gearfinity/gearfinity/planetary_gear_stage/planet_gear_sleeve_bearing-1.step

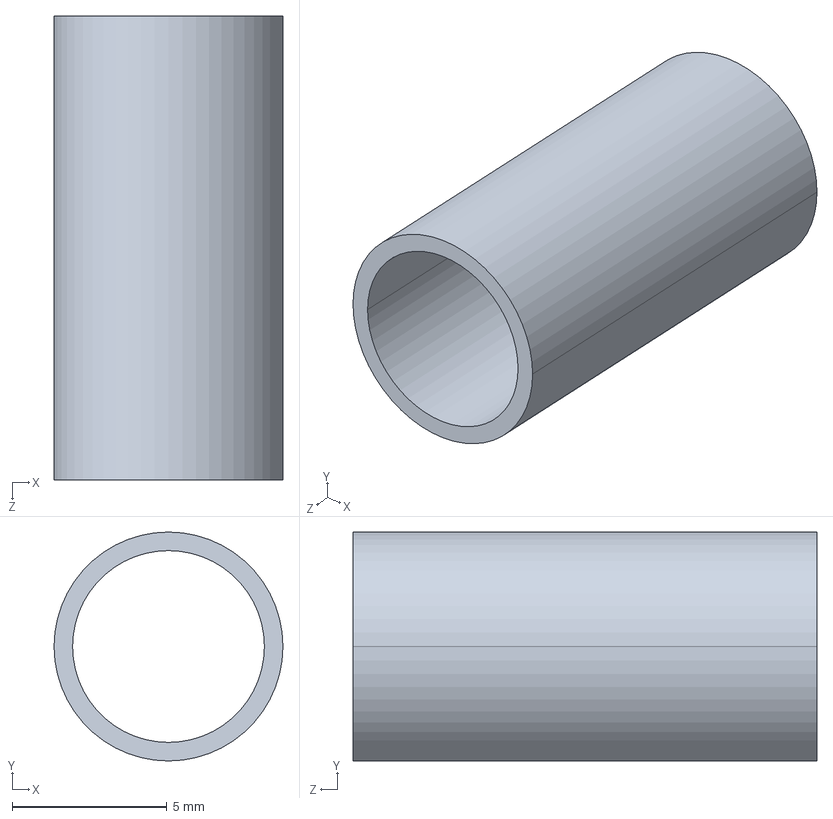
[picture p14: CAD file, 2023-09-10]
planetary_gear_stage/planet_gear_sleeve_bearing-1.step
7.40 x 7.40 x 15.0 mm
