gearfinity/gearfinity/fan_module/fan_cage-1.STL

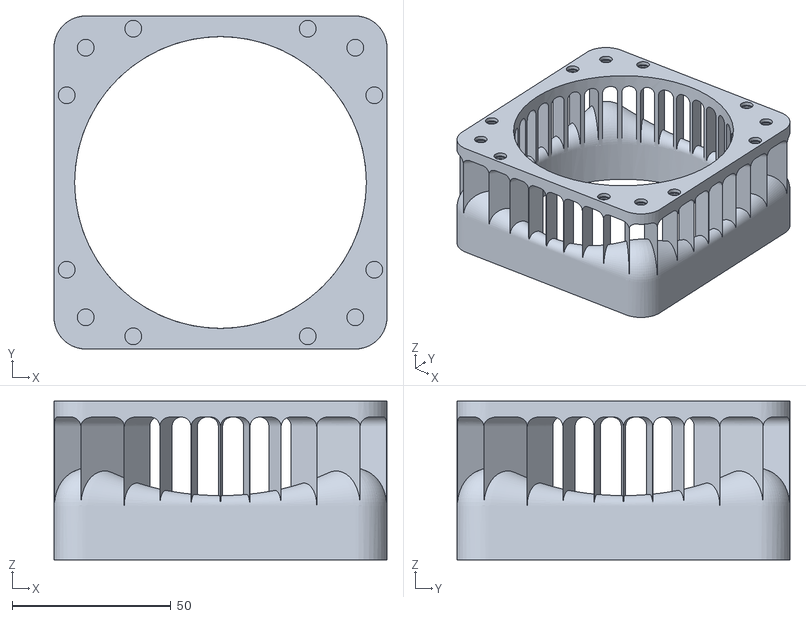
[picture p15: CAD file, 2023-09-10]
fan_module/fan_cage-1.STL
105.0 x 105.0 x 50.0
