gearfinity/gearfinity/planetary_gear_stage/pin-2.step

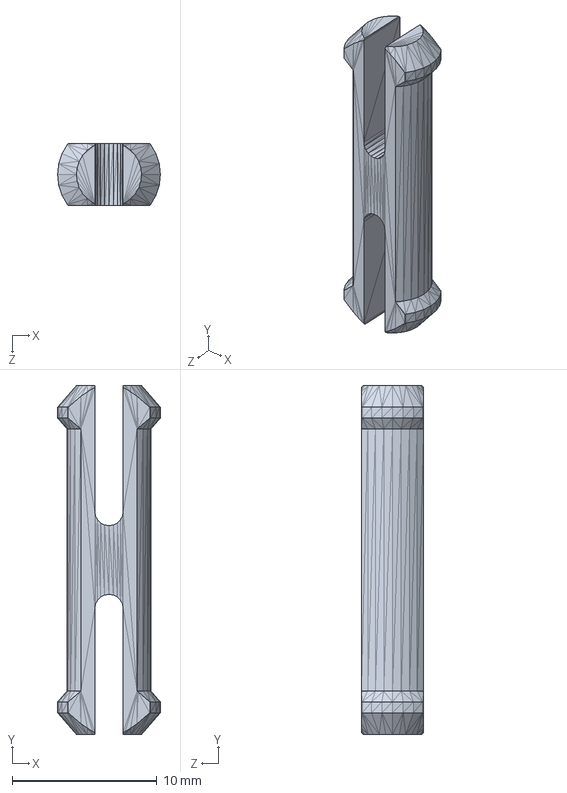
[picture p16: CAD file, 2023-09-10]
planetary_gear_stage/pin-2.step
7.10 x 24.1 x 4.30 mm
