gearfinity/gearfinity/crank_module/crank_shaft_sleeve-1.step

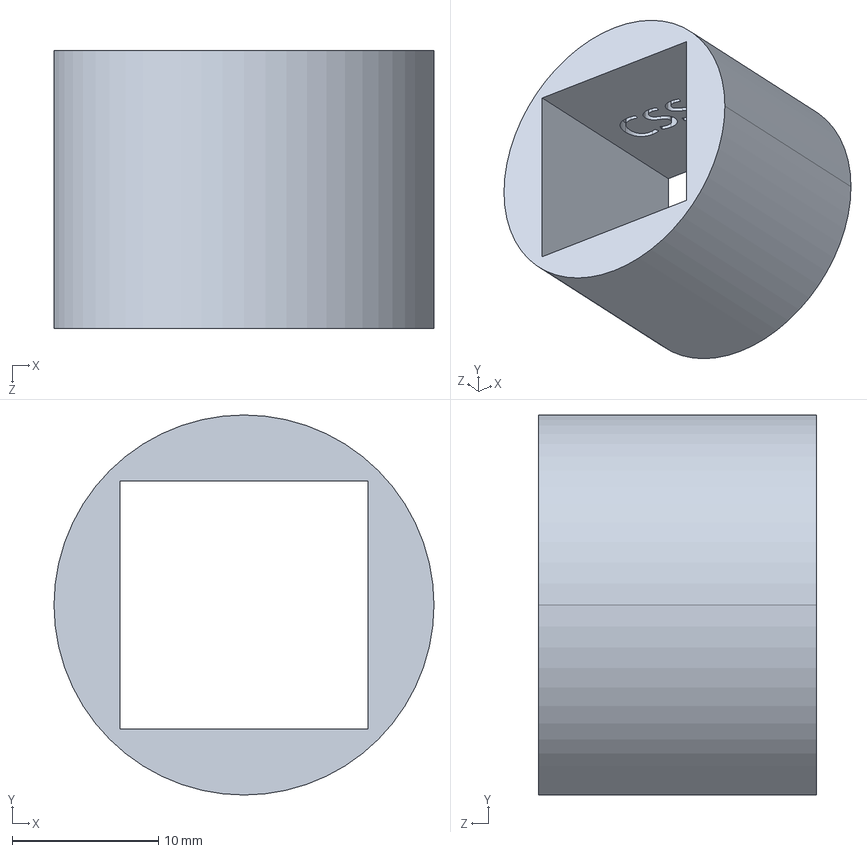
[picture p17: CAD file, 2023-09-10]
crank_module/crank_shaft_sleeve-1.step
26.0 x 26.0 x 19.0 mm
