gearfinity/gearfinity/fan_module/fan_prop_5CC-1.STL

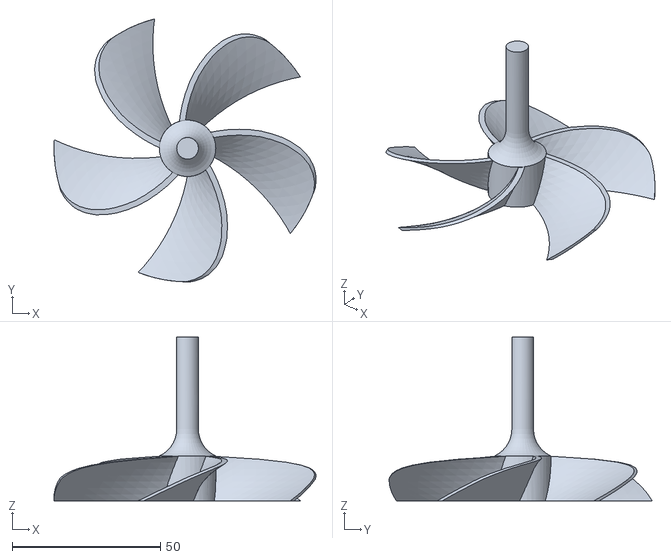
[picture p18: CAD file, 2023-09-10]
fan_module/fan_prop_5CC-1.STL
88.3 x 88.7 x 55.1
