gearfinity/gearfinity/planetary_gear_stage/planet_carrier_top_5-1.step

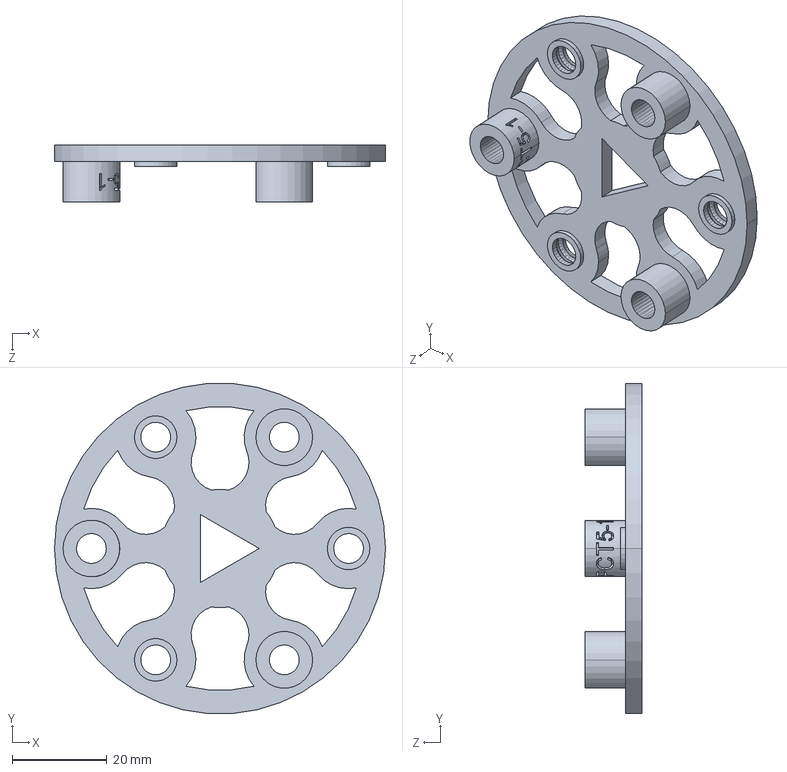
[picture p19: CAD file, 2023-09-10]
planetary_gear_stage/planet_carrier_top_5-1.step
70.0 x 69.8 x 12.0 mm
