gearfinity/gearfinity/crank_module/pin-1.step

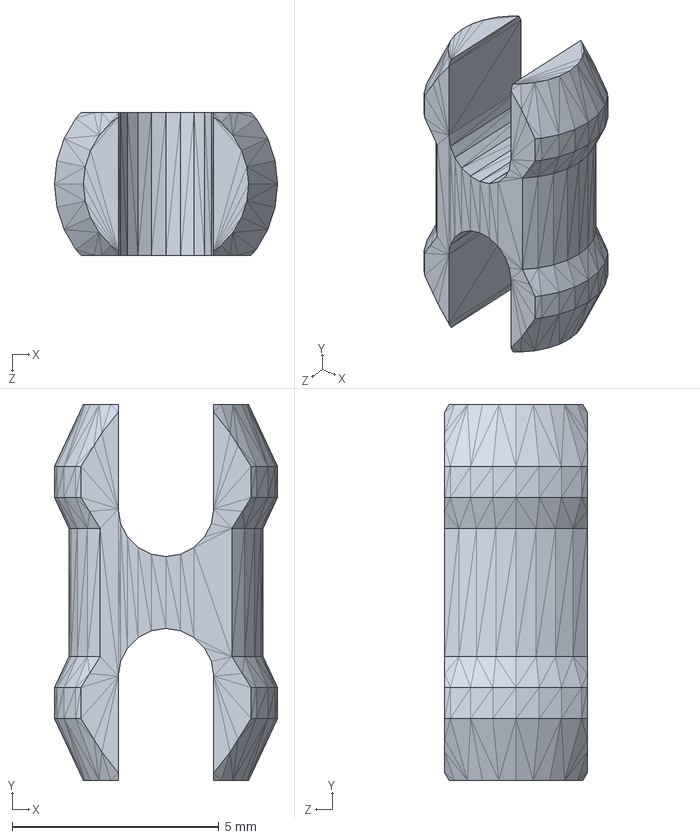
[picture p20: CAD file, 2023-09-10]
crank_module/pin-1.step
5.40 x 9.10 x 3.45 mm
