gearfinity/gearfinity/planetary_gear_stage/planetary_gear_core_5-2S15.STL

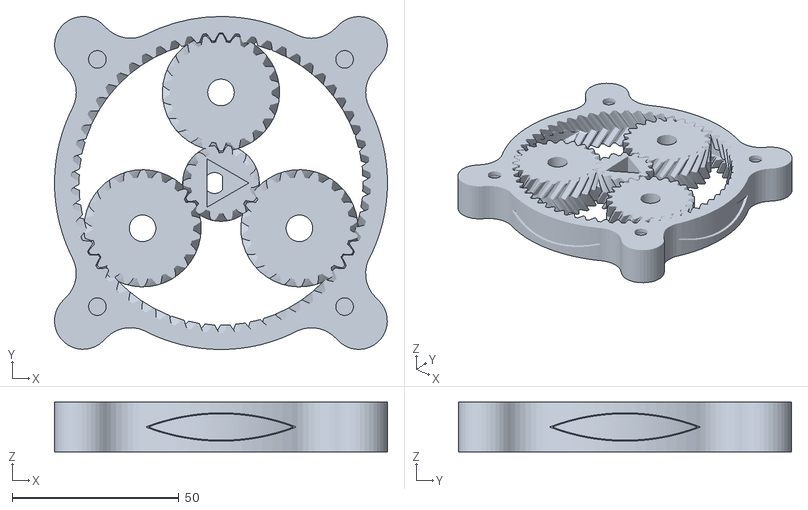
[picture p21: CAD file, 2023-09-10]
planetary_gear_stage/planetary_gear_core_5-2S15.STL
100.0 x 100.0 x 15.0
