gearfinity/gearfinity/crank_module/drive_shaft_5-3.step

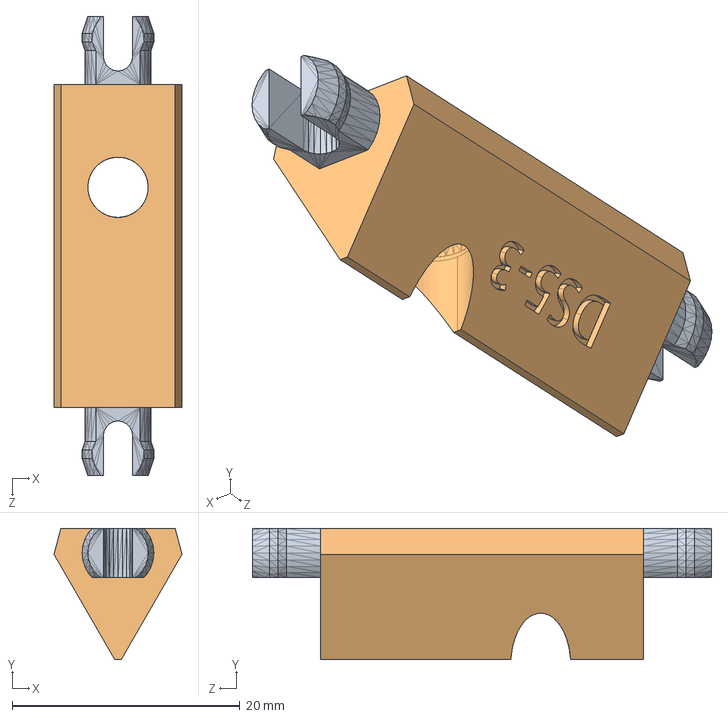
[picture p22: CAD file, 2023-09-10]
crank_module/drive_shaft_5-3.step
11.2 x 11.5 x 40.3 mm
