gearfinity/gearfinity/fan_module/drive_shaft_5-4.step

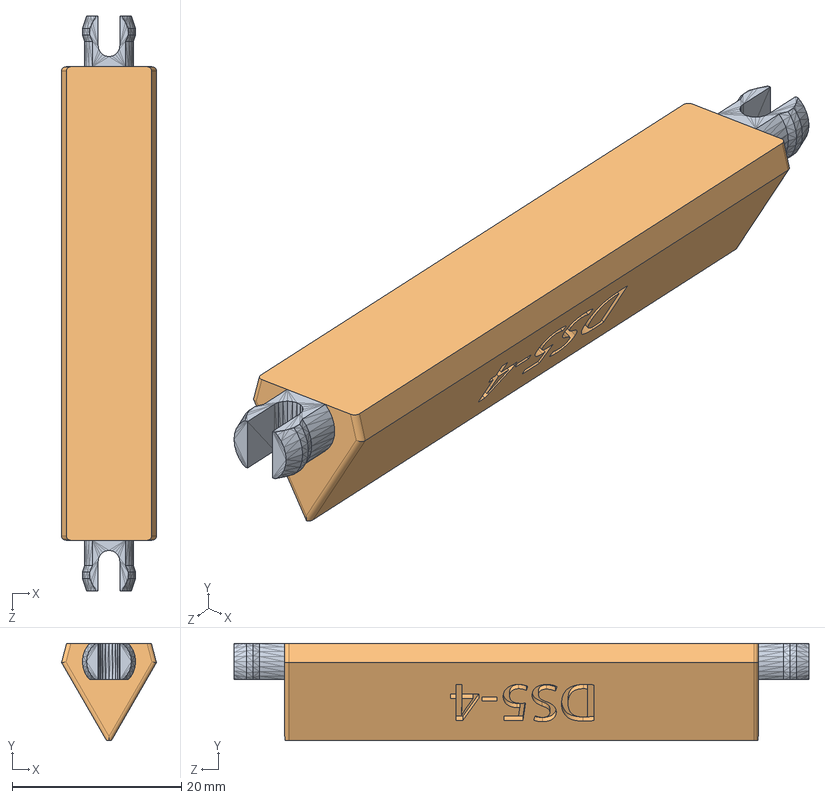
[picture p23: CAD file, 2023-09-10]
fan_module/drive_shaft_5-4.step
11.2 x 11.5 x 68.0 mm
