gearfinity/gearfinity/planetary_gear_stage/planet_carrier_bottom_5-1.STL

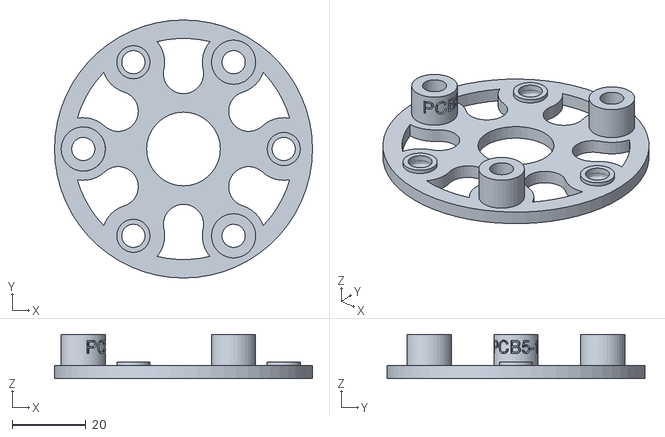
[picture p24: CAD file, 2023-09-10]
planetary_gear_stage/planet_carrier_bottom_5-1.STL
70.0 x 70.0 x 12.0
