gearfinity/gearfinity/fan_module/roller_bearing-1.STL

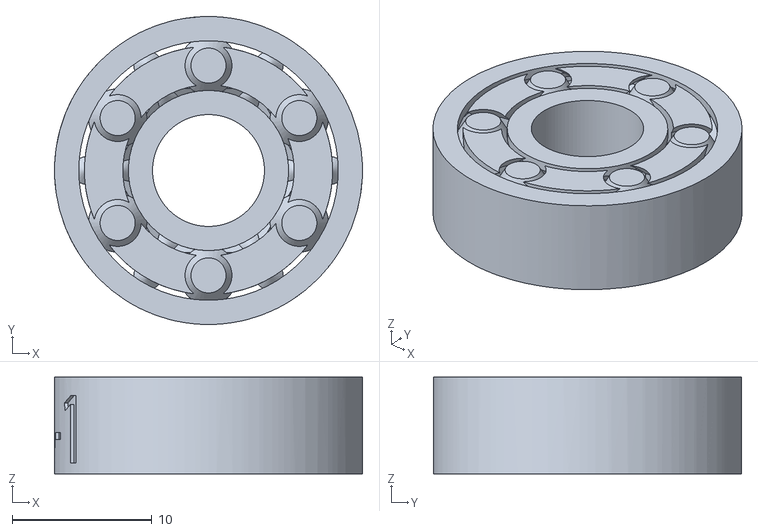
[picture p25: CAD file, 2023-09-10]
fan_module/roller_bearing-1.STL
22.0 x 22.0 x 6.90
