gearfinity/gearfinity/_all_parts/handle_plate_bracket_3.STL

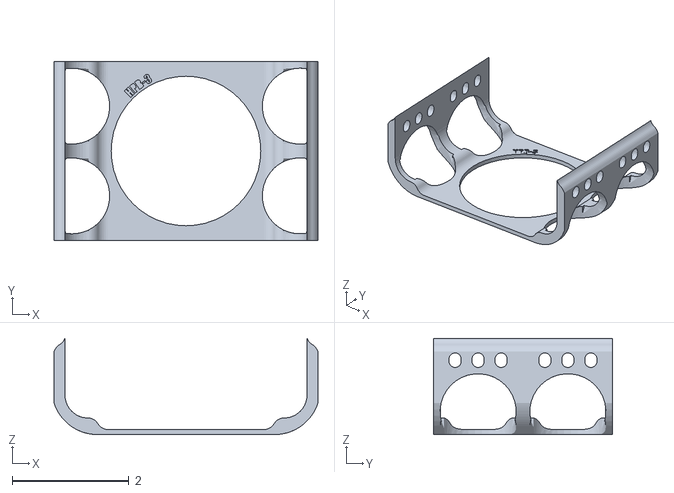
[picture p26: CAD file, 2025-04-01]
_all_parts/handle_plate_bracket_3.STL
4.52 x 3.07 x 1.65
