gearfinity/gearfinity/crank_module/handle_plate-1.STL

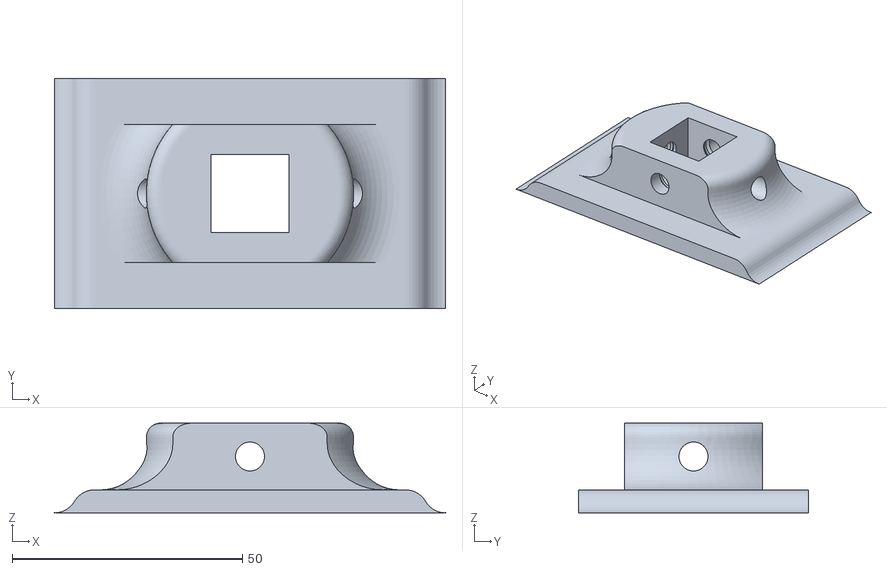
[picture p27: CAD file, 2023-09-10]
crank_module/handle_plate-1.STL
84.9 x 50.0 x 19.5
