gearfinity/gearfinity/_all_parts/handle_plate-3.STL

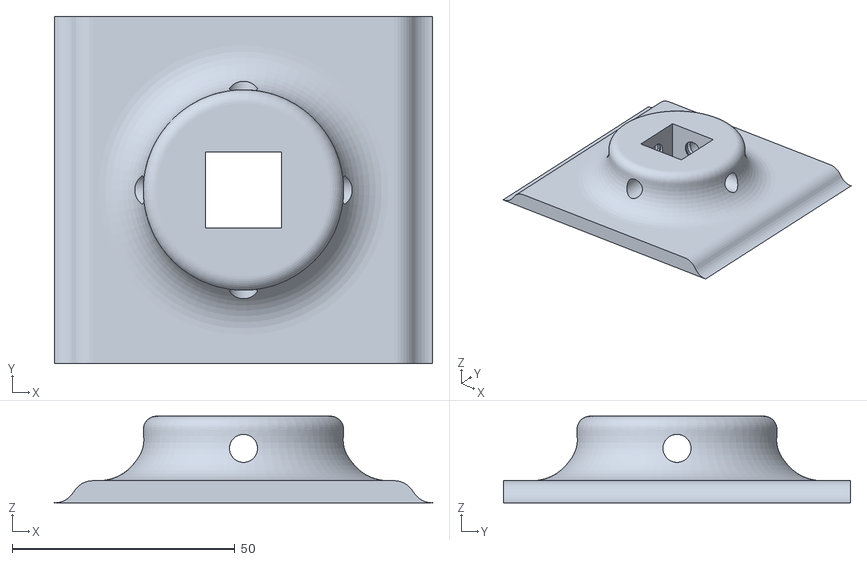
[picture p28: CAD file, 2025-04-01]
_all_parts/handle_plate-3.STL
84.9 x 78.0 x 19.5
