gearfinity/gearfinity/crank_module/gearbox_cover_2_stage-1.STL

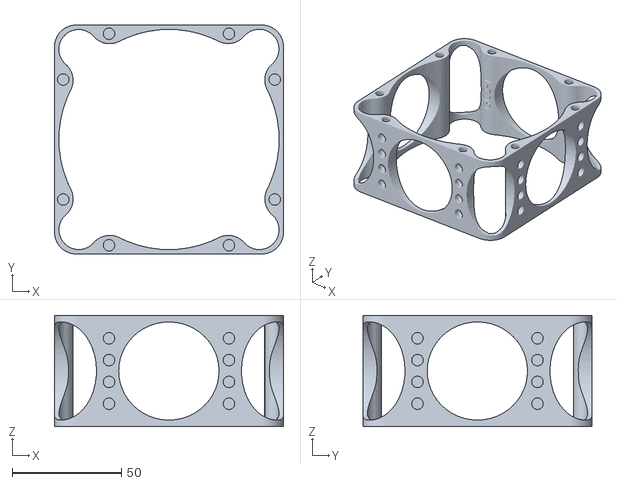
[picture p29: CAD file, 2023-09-10]
crank_module/gearbox_cover_2_stage-1.STL
105.0 x 105.0 x 51.0
