gearfinity/gearfinity/fan_module/crank_handle-2.STL

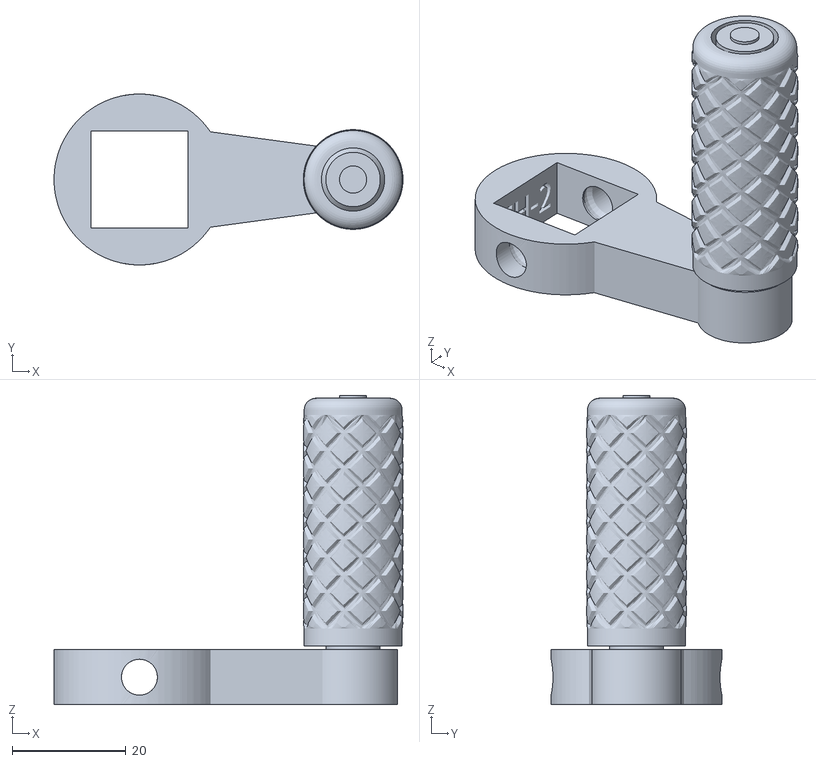
[picture p30: CAD file, 2023-09-10]
fan_module/crank_handle-2.STL
61.3 x 30.0 x 54.3
