gearfinity/gearfinity/_all_parts/handle_plate-2.STL

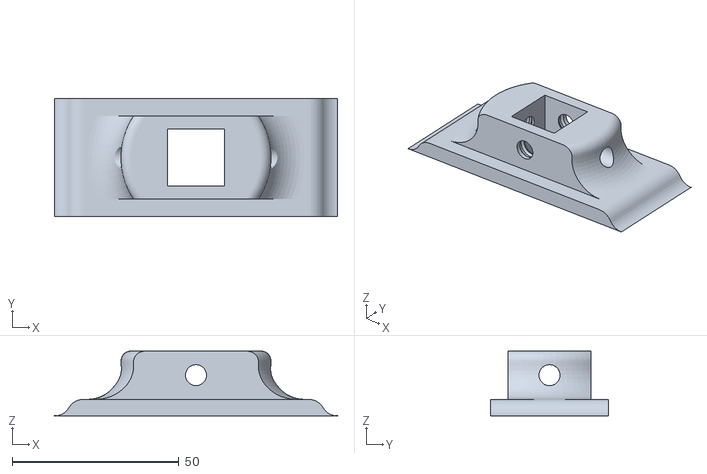
[picture p31: CAD file, 2025-04-01]
_all_parts/handle_plate-2.STL
84.9 x 35.5 x 19.5
