gearfinity/gearfinity/_all_parts/gearbox_cover_3_stage-1.STL

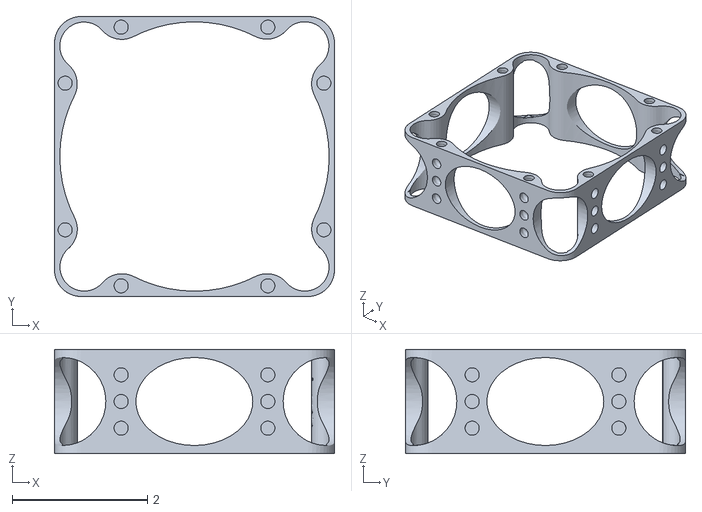
[picture p32: CAD file, 2025-04-01]
_all_parts/gearbox_cover_3_stage-1.STL
4.13 x 4.13 x 1.54
