gearfinity/gearfinity/crank_module/planetary_gear_core_5-2S15.step

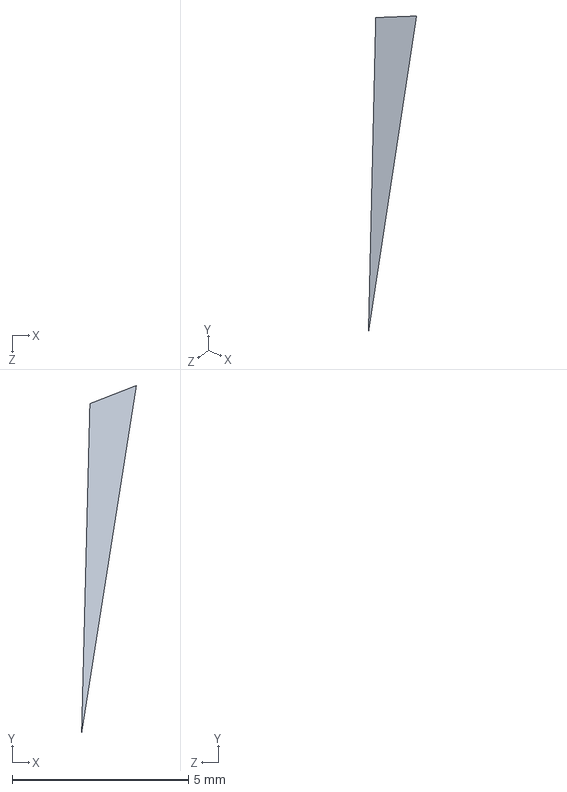
[picture p33: CAD file, 2023-09-09]
crank_module/planetary_gear_core_5-2S15.step
1.55 x 9.86 x 0 mm
