gearfinity/gearfinity/crank_module/planet_carrier_bottom_5-1.step

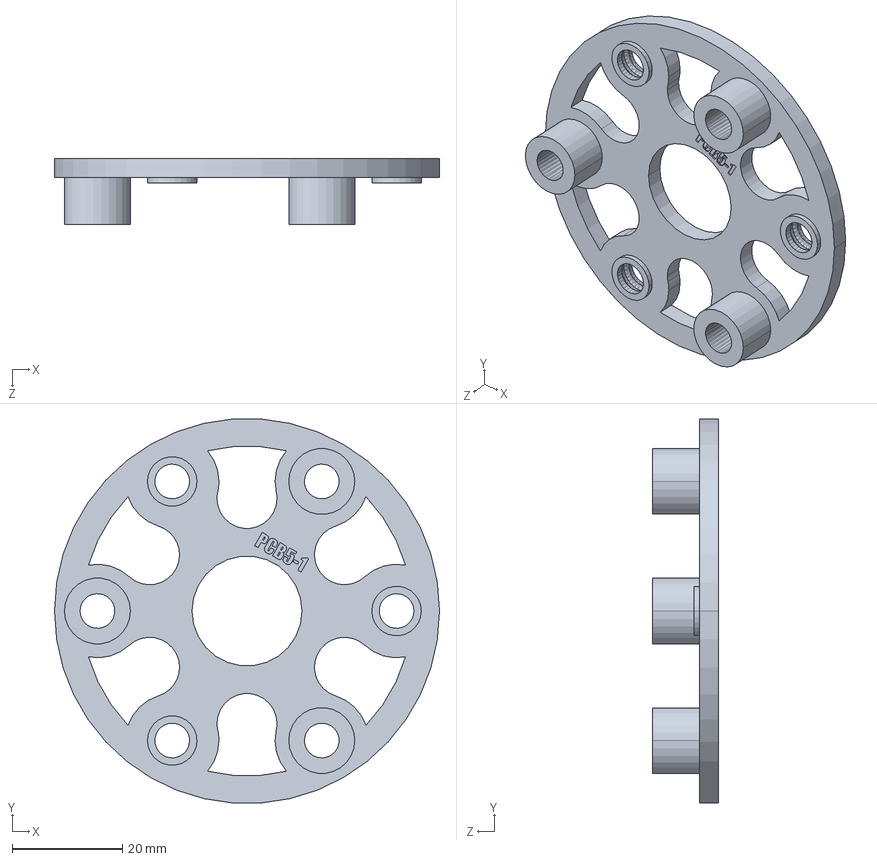
[picture p35: CAD file, 2023-07-14]
crank_module/planet_carrier_bottom_5-1.step
70.0 x 69.8 x 12.0 mm
