gearfinity/gearfinity/_all_parts/handle_plate_bracket_half-2.STL

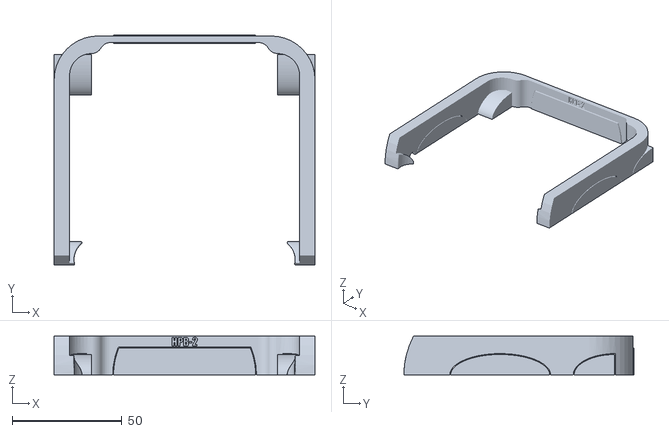
[picture p36: CAD file, 2025-04-01]
_all_parts/handle_plate_bracket_half-2.STL
119.0 x 105.0 x 17.8
