gearfinity/gearfinity/_all_parts/planetary_gear_core_5-3S15.STL

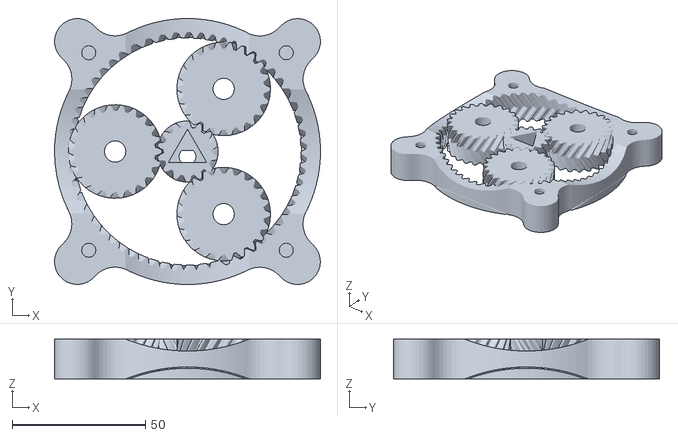
[picture p37: CAD file, 2025-04-01]
_all_parts/planetary_gear_core_5-3S15.STL
100.0 x 100.0 x 15.0
