gearfinity/gearfinity/_all_parts/drive_shaft_5-3-2.SLDPRT

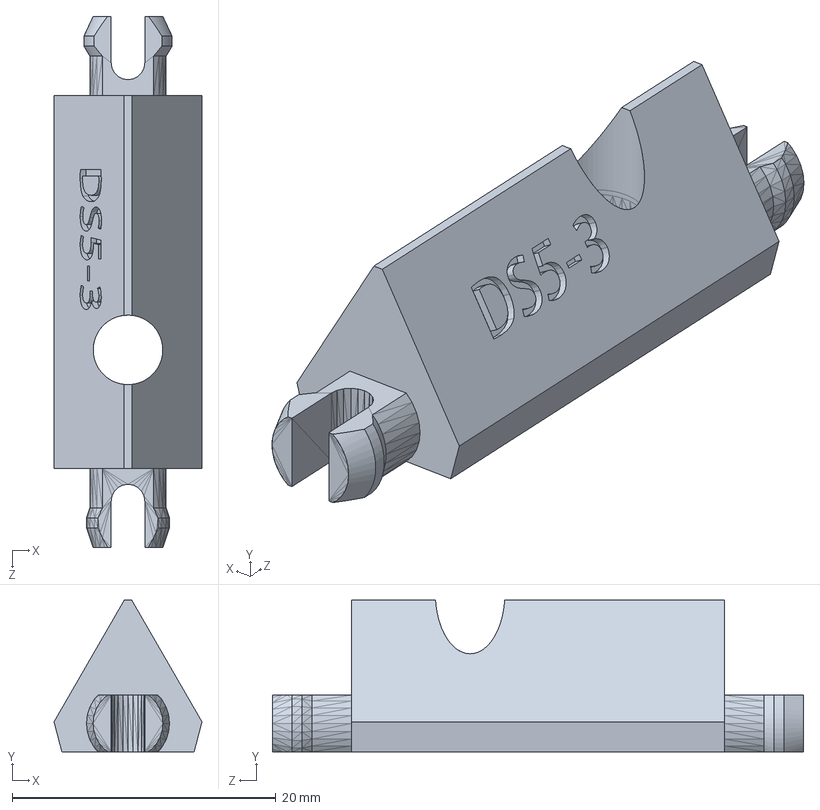
[picture p38: CAD file, 2024-07-02]
_all_parts/drive_shaft_5-3-2.SLDPRT
11.2 x 11.5 x 40.3 mm
