gearfinity/gearfinity/_all_parts/crank_arm-1.STL

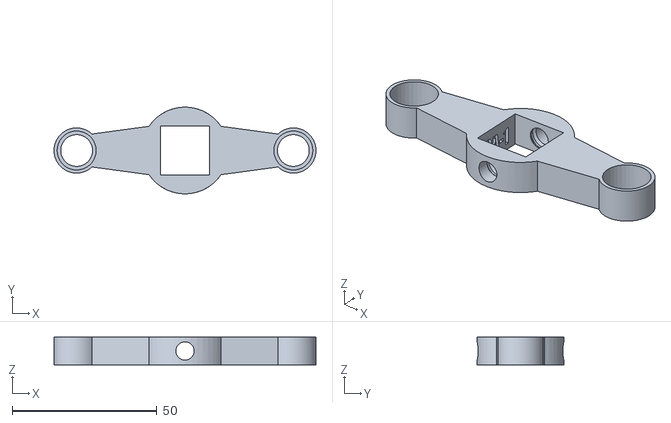
[picture p39: CAD file, 2024-07-02]
_all_parts/crank_arm-1.STL
90.7 x 30.0 x 9.66
