gearfinity/gearfinity/_all_parts/crank_spindle-1.SLDPRT

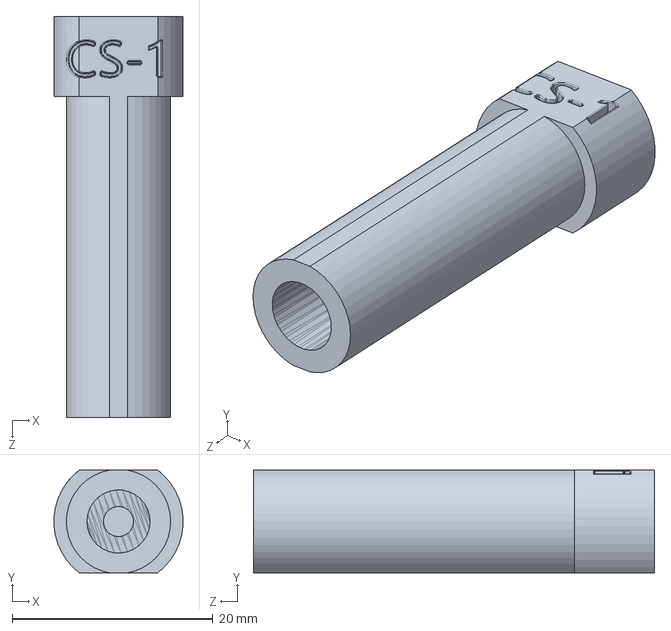
[picture p40: CAD file, 2024-07-02]
_all_parts/crank_spindle-1.SLDPRT
12.9 x 10.2 x 40.0 mm
