gearfinity/gearfinity/_all_parts/crank_arm-2.STL

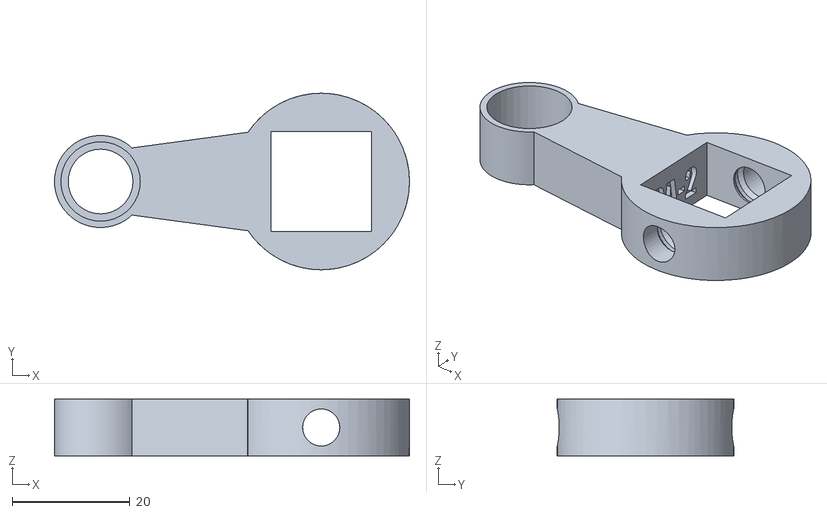
[picture p41: CAD file, 2024-07-02]
_all_parts/crank_arm-2.STL
60.3 x 30.0 x 9.66
