gearfinity/gearfinity/_all_parts/crank_handle-grip-1.STL

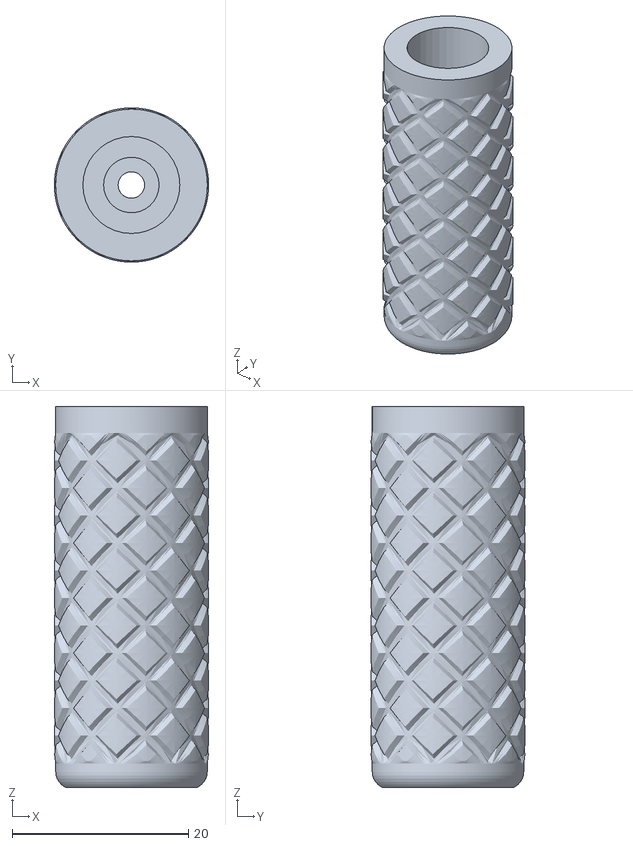
[picture p42: CAD file, 2024-07-02]
_all_parts/crank_handle-grip-1.STL
17.5 x 17.5 x 43.2
