gearfinity/gearfinity/_all_parts/handle_plate_bracket_half-1.3MF

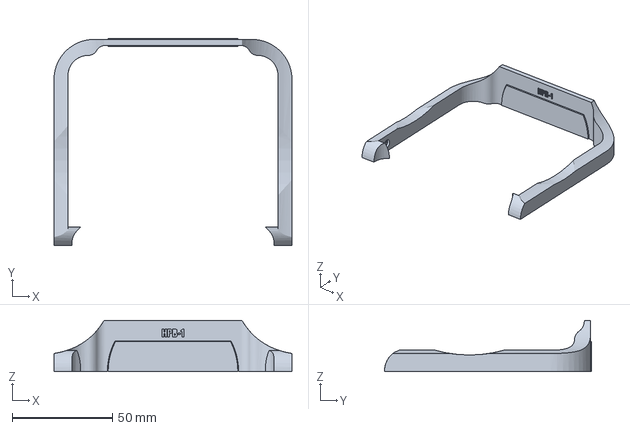
[picture p43: CAD file, 2024-07-01]
_all_parts/handle_plate_bracket_half-1.3MF
118.9 x 103.5 x 25.5 mm
