gearfinity/gearfinity/_all_parts/planetary_gear_stage_core_bearing_5_tol_15_gear_mesh_ring.SLDPRT

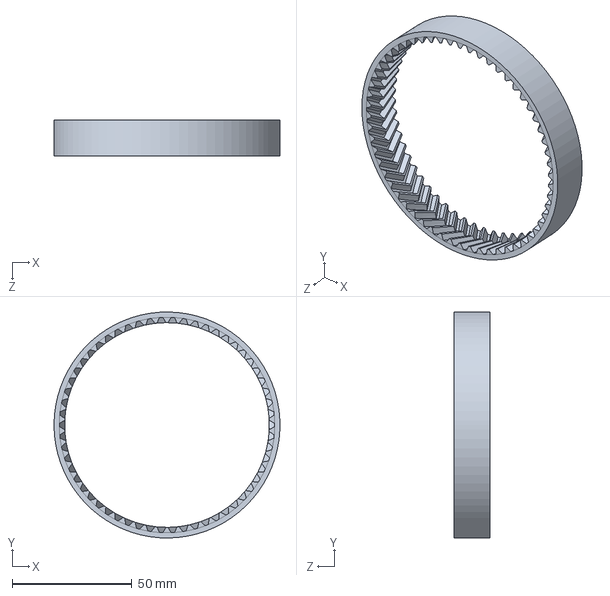
[picture p44: CAD file, 2023-07-14]
_all_parts/planetary_gear_stage_core_bearing_5_tol_15_gear_mesh_ring.SLDPRT
94.2 x 94.2 x 15.0 mm
