gearfinity/gearfinity/_all_parts/planetary_gear_stage_core_bearing_5_tol_15_gear_mesh_sun.SLDPRT

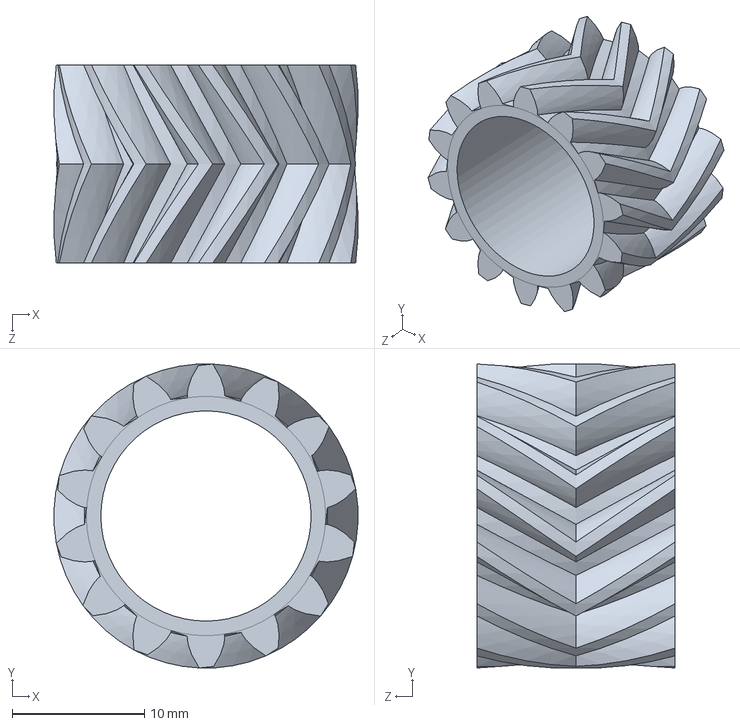
[picture p45: CAD file, 2023-07-14]
_all_parts/planetary_gear_stage_core_bearing_5_tol_15_gear_mesh_sun.SLDPRT
23.0 x 23.0 x 15.0 mm
