gearfinity/gearfinity/_all_parts/planet_pinhole_profile.SLDPRT

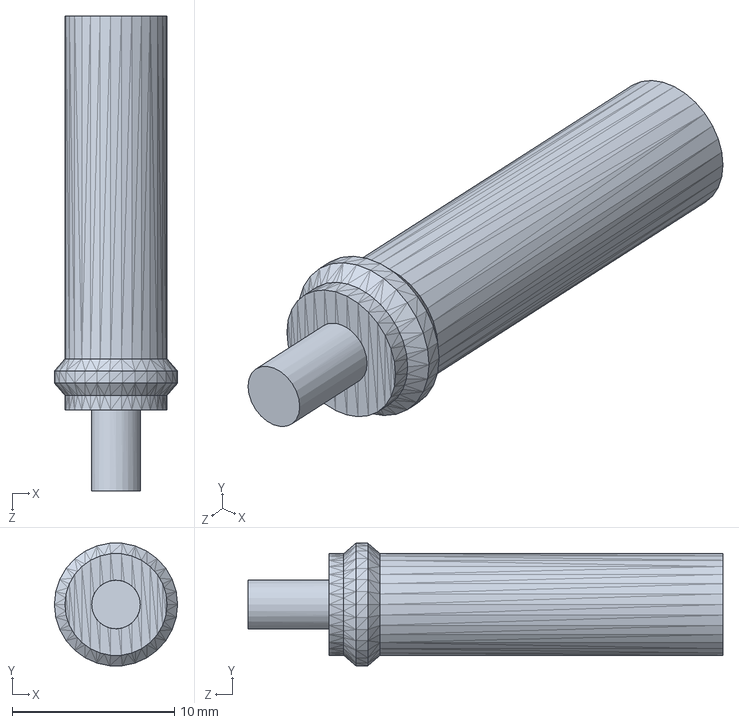
[picture p46: CAD file, 2023-07-14]
_all_parts/planet_pinhole_profile.SLDPRT
7.60 x 7.56 x 29.3 mm
