gearfinity/gearfinity/_all_parts/plate_pinhole_profile.SLDPRT

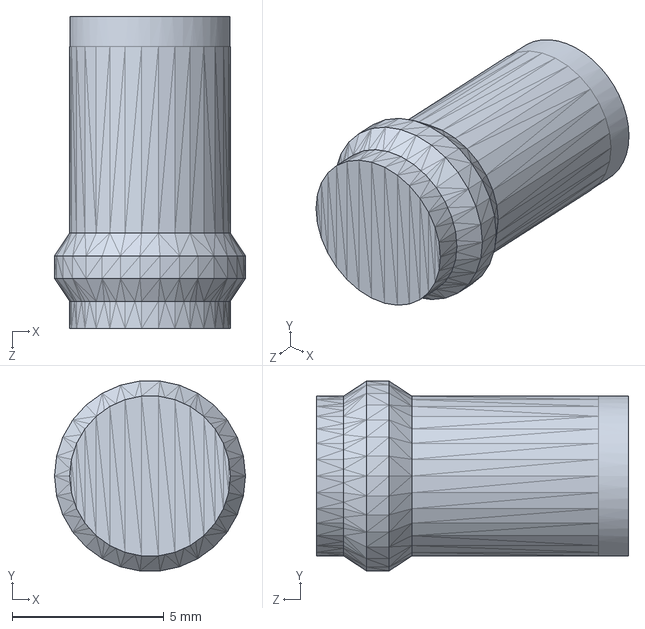
[picture p47: CAD file, 2023-07-14]
_all_parts/plate_pinhole_profile.SLDPRT
6.30 x 6.27 x 10.3 mm
