gearfinity/gearfinity/_all_parts/blank_cylinder.SLDPRT

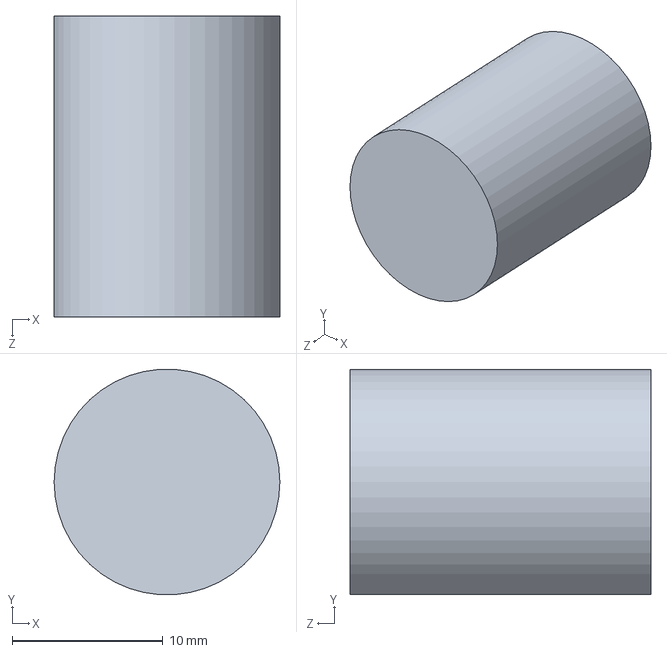
[picture p48: CAD file, 2023-07-14]
_all_parts/blank_cylinder.SLDPRT
15.0 x 15.0 x 20.0 mm
