gearfinity/gearfinity/_all_parts/planetary_gear_stage_core_bearing_5_tol_15_gear_mesh_planet3.SLDPRT

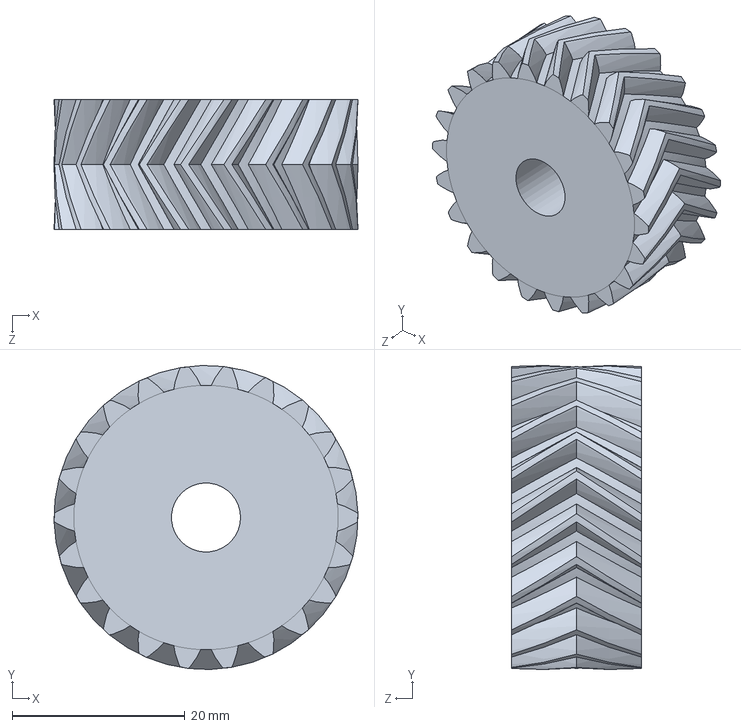
[picture p49: CAD file, 2023-07-14]
_all_parts/planetary_gear_stage_core_bearing_5_tol_15_gear_mesh_planet3.SLDPRT
35.2 x 35.2 x 15.0 mm
