gearfinity/gearfinity/_all_parts/plate_pinhole_profile_v2.SLDPRT

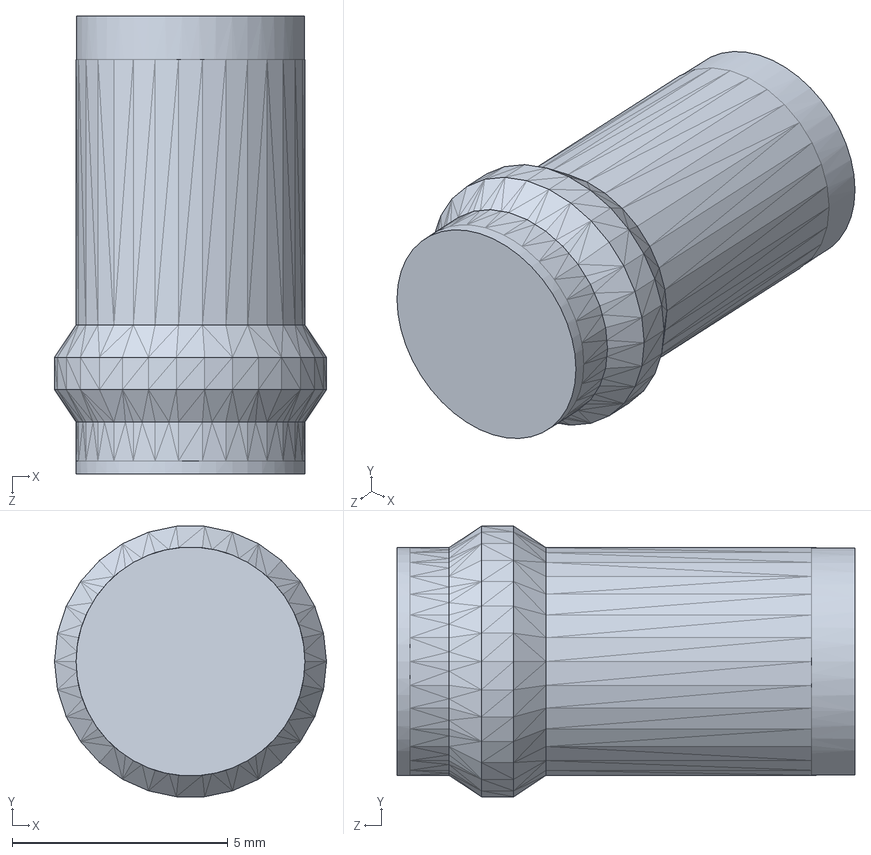
[picture p50: CAD file, 2023-07-14]
_all_parts/plate_pinhole_profile_v2.SLDPRT
6.30 x 6.27 x 10.6 mm
